dtomcat/AdvancedXeniumProgrammer/images/bitbus2flash.png

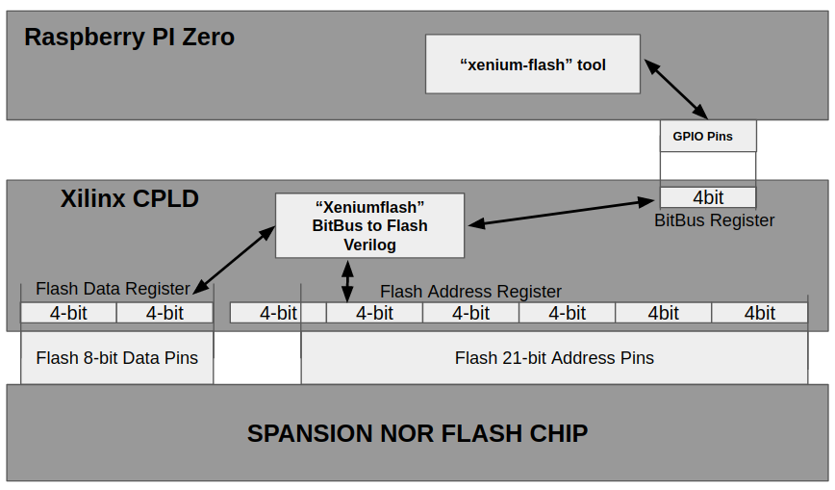
images/bitbus2flash.png
