dtomcat/AdvancedXeniumProgrammer/images/bitbus.png

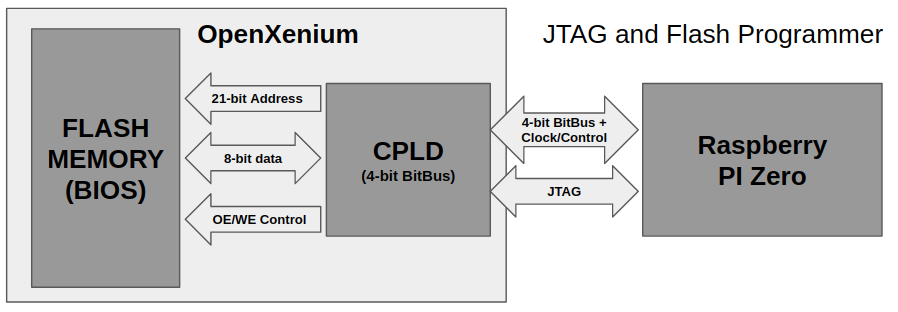
images/bitbus.png
