dtomcat/AdvancedXeniumProgrammer/images/boot.png

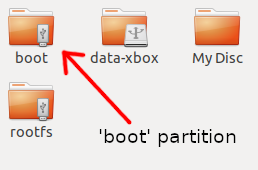
images/boot.png
