dtomcat/AdvancedXeniumProgrammer/images/connections-omega.png

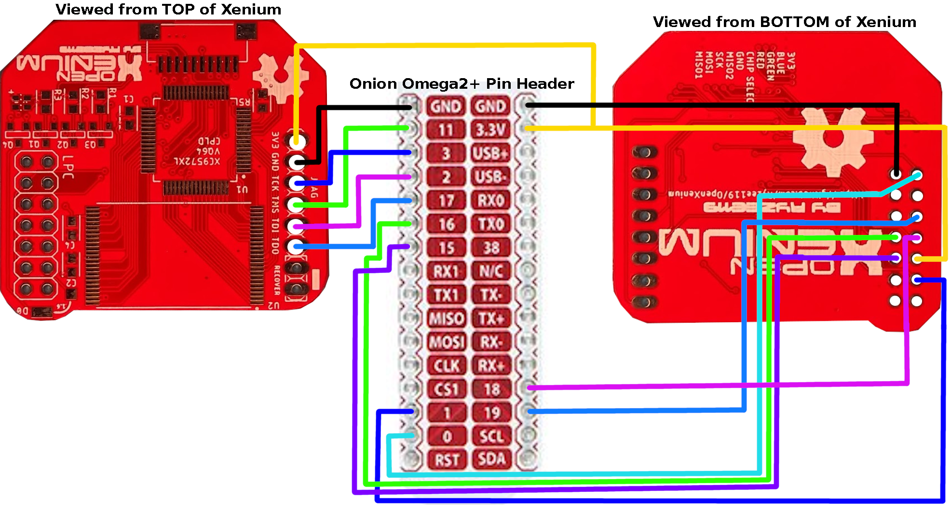
images/connections-omega.png
