dtomcat/AdvancedXeniumProgrammer/images/connections-pi.png

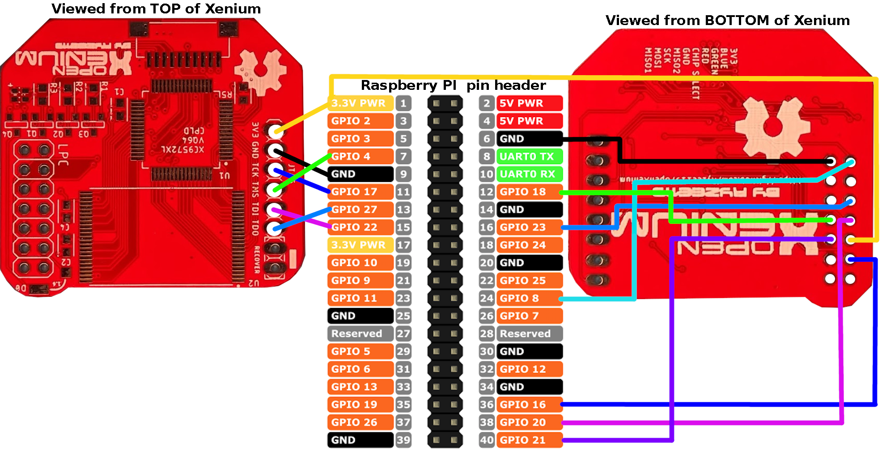
images/connections-pi.png
