dtomcat/AdvancedXeniumProgrammer/images/mcpx-lpc.png

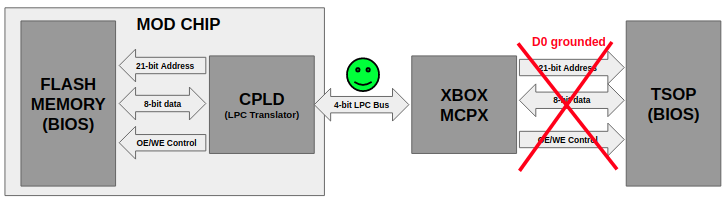
images/mcpx-lpc.png
