dtomcat/AdvancedXeniumProgrammer/images/openxenium2.jpg

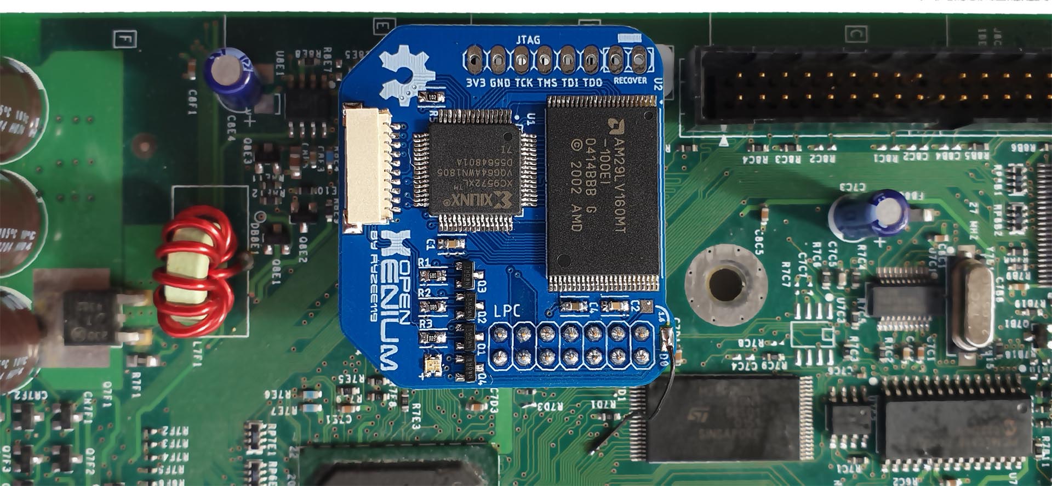
images/openxenium2.jpg
