dtomcat/AdvancedXeniumProgrammer/images/openxenium.jpg

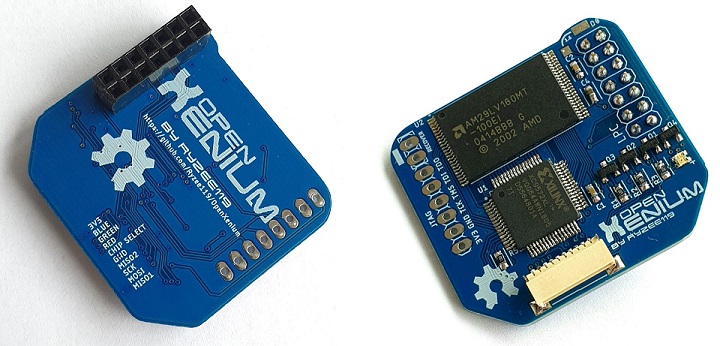
images/openxenium.jpg
