dtomcat/AdvancedXeniumProgrammer/images/pi-spi.jpg

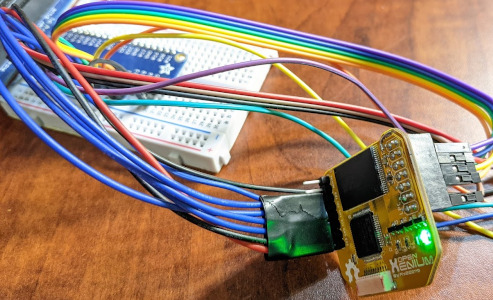
images/pi-spi.jpg
