dtomcat/AdvancedXeniumProgrammer/images/pi-wifi.png

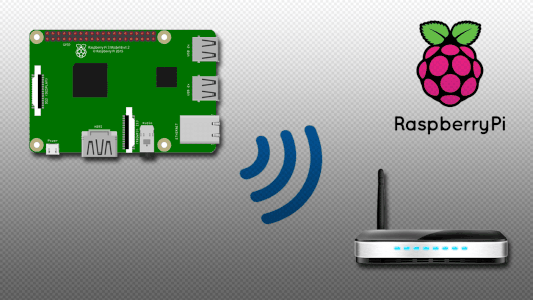
images/pi-wifi.png
