dtomcat/AdvancedXeniumProgrammer/images/pinout-omega.png

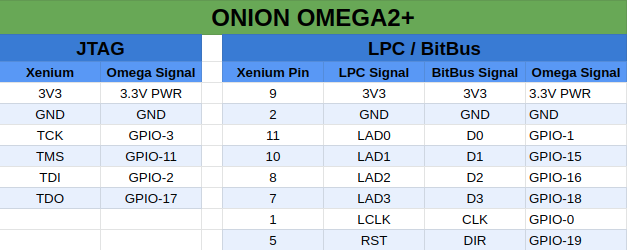
images/pinout-omega.png
