dtomcat/AdvancedXeniumProgrammer/images/pinout-pi.png

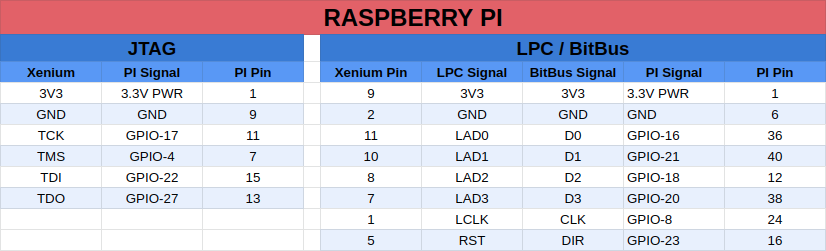
images/pinout-pi.png
