dtomcat/AdvancedXeniumProgrammer/images/xenium-os.jpg

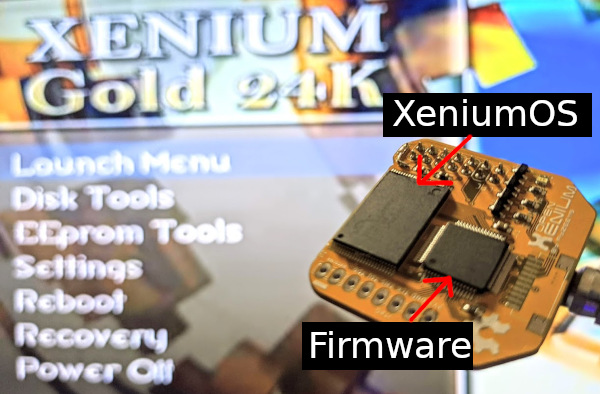
images/xenium-os.jpg
