dtomcat/AdvancedXeniumProgrammer/images/xilinx-programmer.jpg

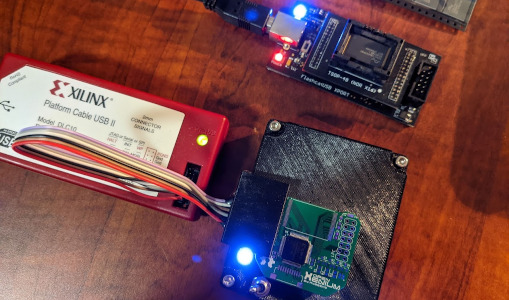
images/xilinx-programmer.jpg
